marcelomaurin/Temperatura/imgs/main.png

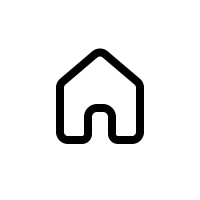
imgs/main.png
