marcelomaurin/Temperatura/imgs/sensores.png

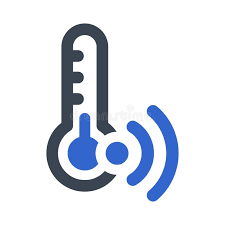
imgs/sensores.png
