marcelomaurin/Temperatura/software/img/cad_device.png

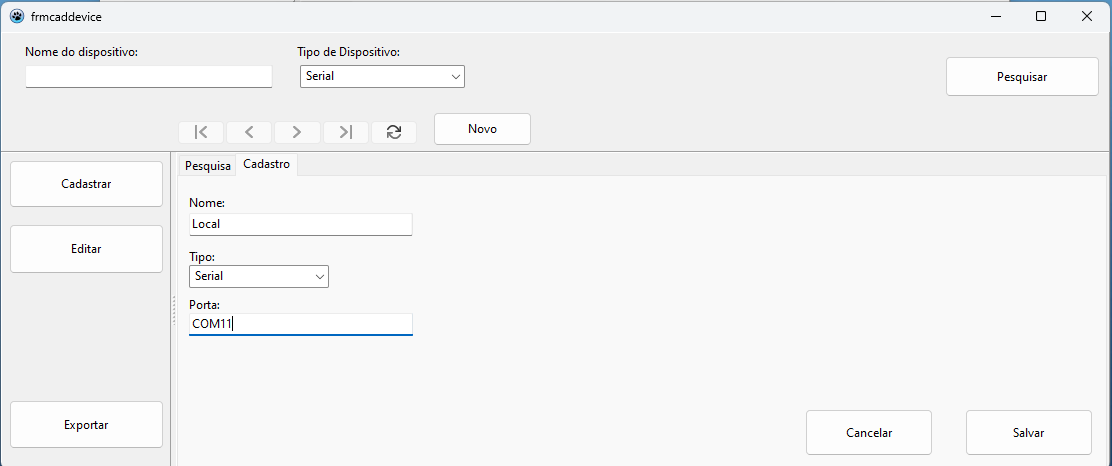
software/img/cad_device.png
