marcelomaurin/Temperatura/software/img/instalador_tela01.png

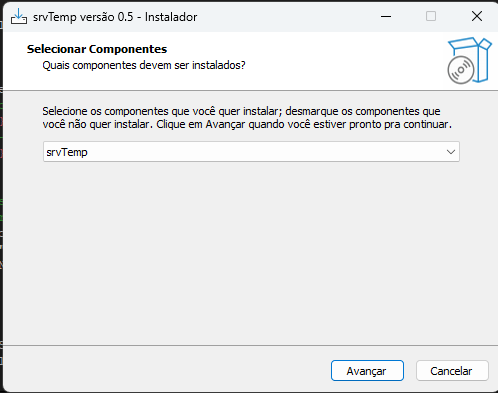
software/img/instalador_tela01.png
