marcelomaurin/Temperatura/software/img/pesq_device.png

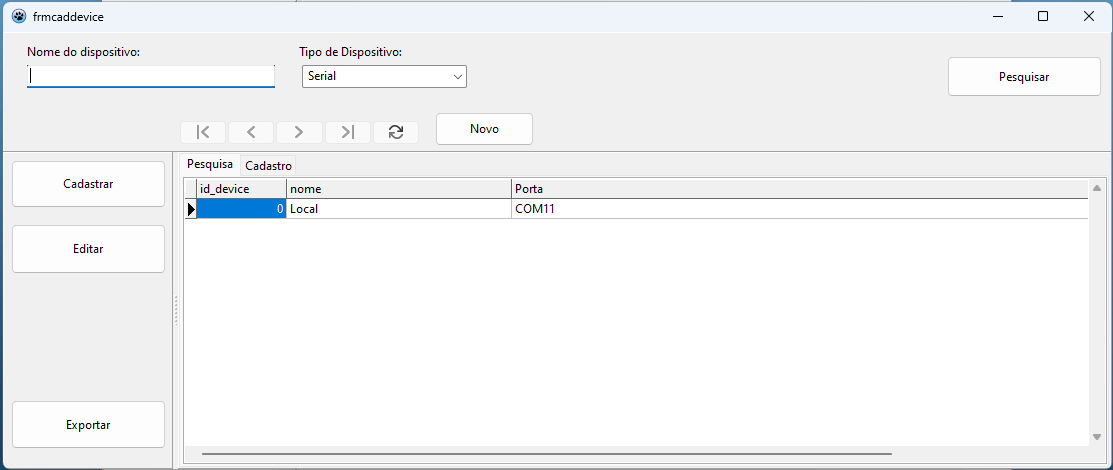
software/img/pesq_device.png
